hallard/RAK831-Zero/pictures/PiZero-RAK831-bot.jpg

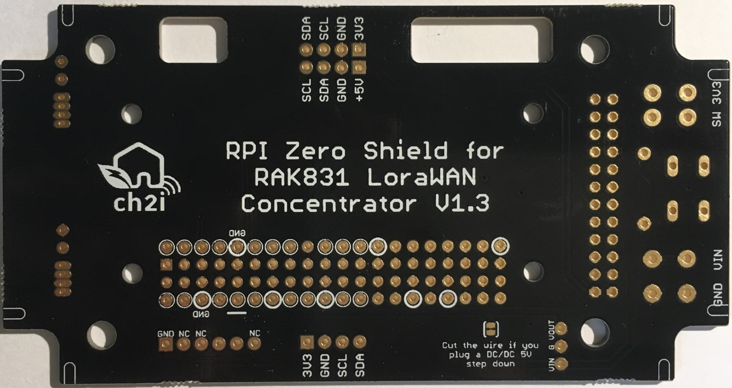
pictures/PiZero-RAK831-bot.jpg
