hallard/RAK831-Zero/pictures/RAK831_Zero.jpg

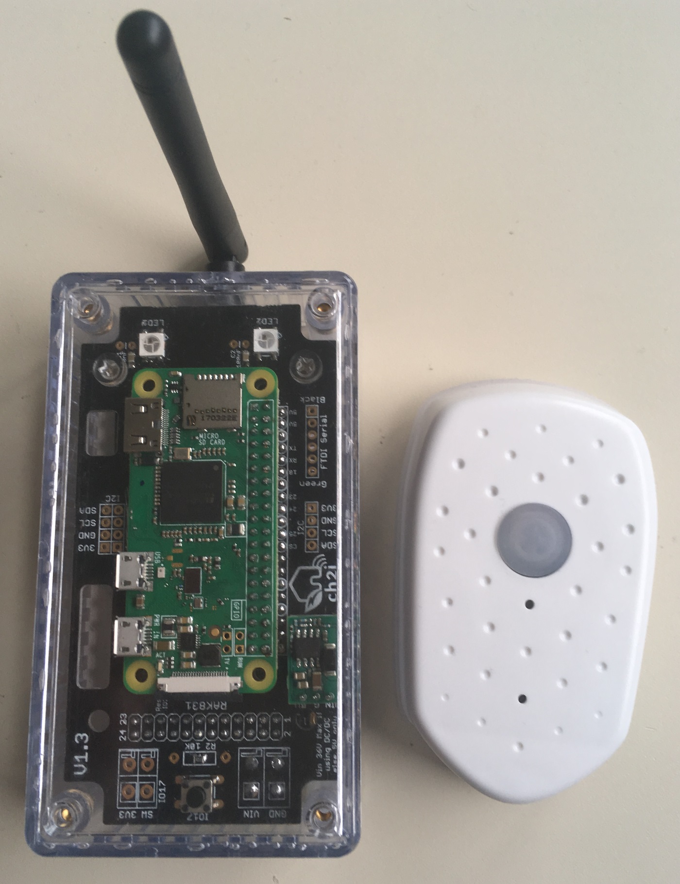
pictures/RAK831_Zero.jpg
